sampidevkit/PIC32DevKit/Docs/PIC32DevKit Diagram-PartNumber.png

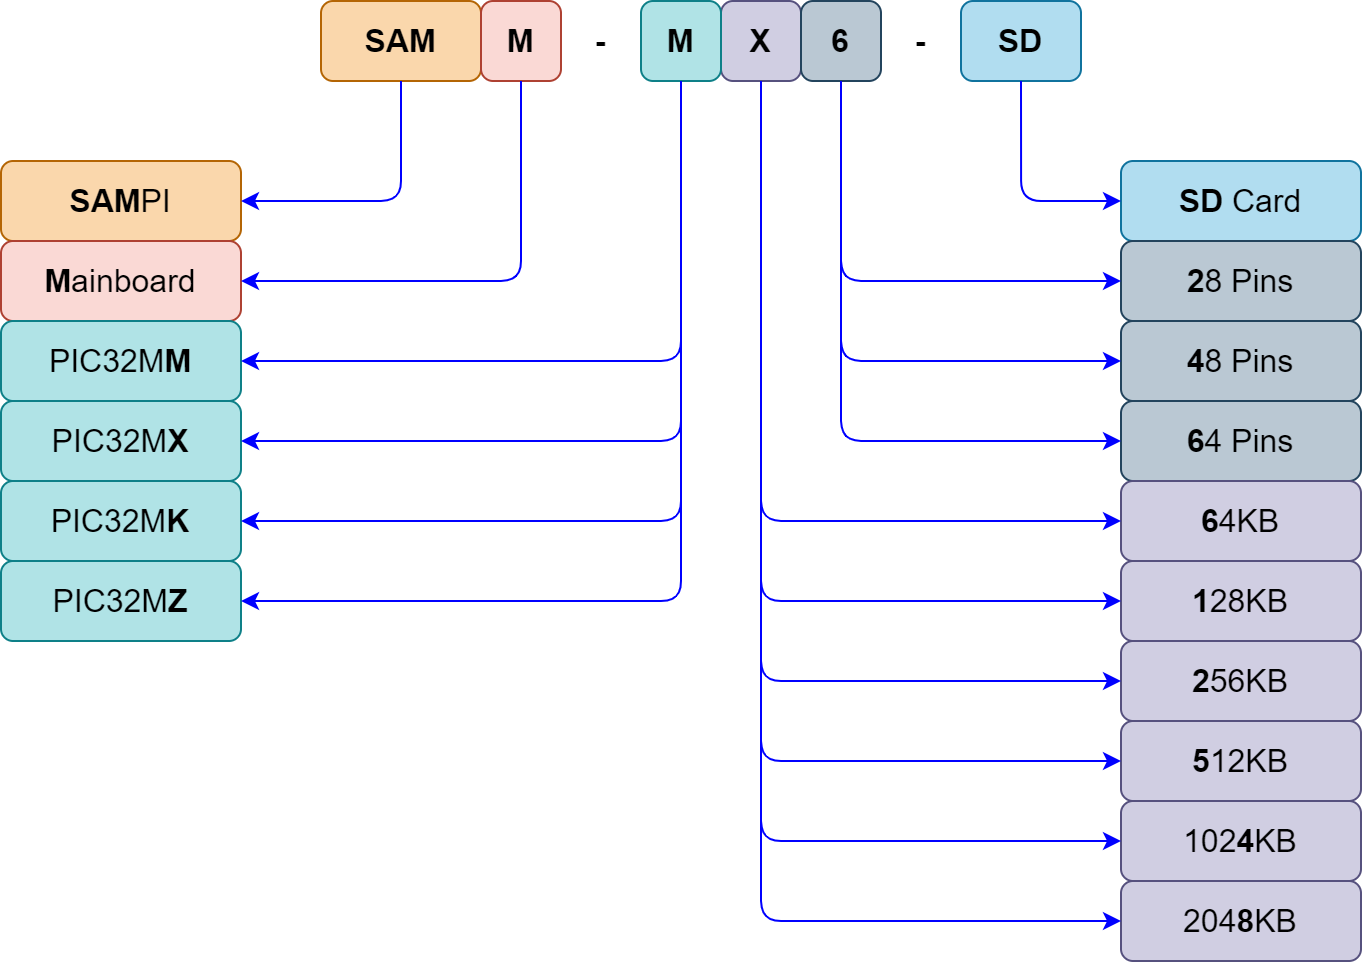
Docs/PIC32DevKit Diagram-PartNumber.png
