sampidevkit/PIC32DevKit/Docs/PIC32DevKit.png

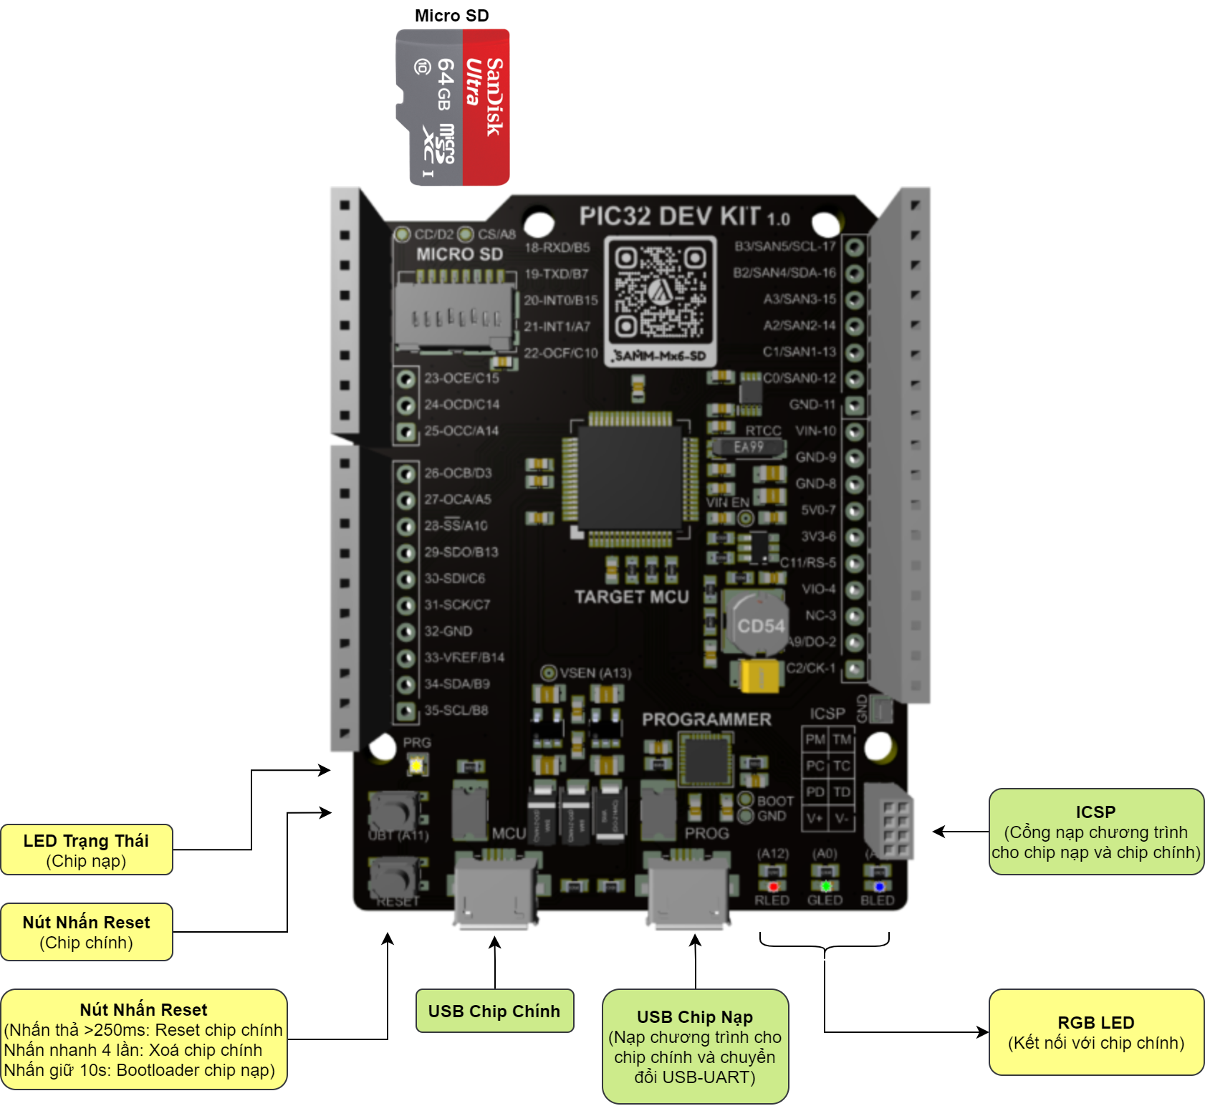
Docs/PIC32DevKit.png
