sampidevkit/PIC32DevKit/Docs/Ultra_microSDXC_UHS-I_Class10_64GB-retina.png

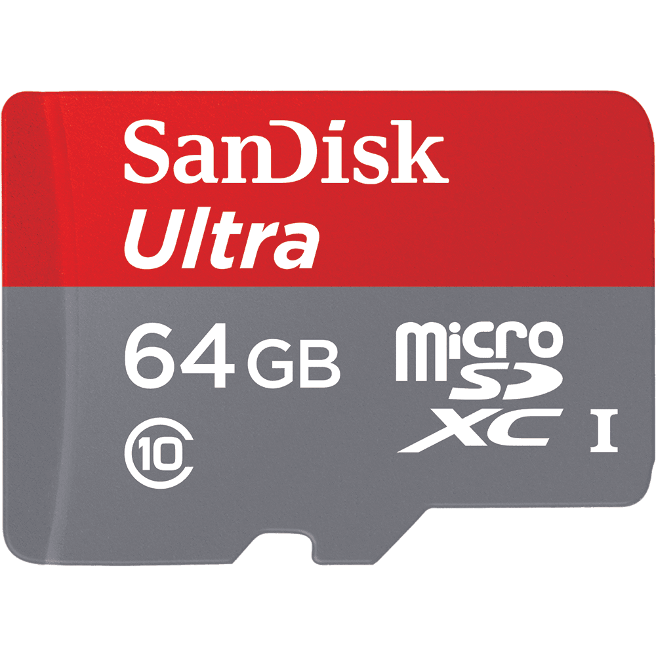
Docs/Ultra_microSDXC_UHS-I_Class10_64GB-retina.png
