sampidevkit/PIC32DevKit/HW/Product/V2.0/Picture/ScreenShot_20220208212343.png

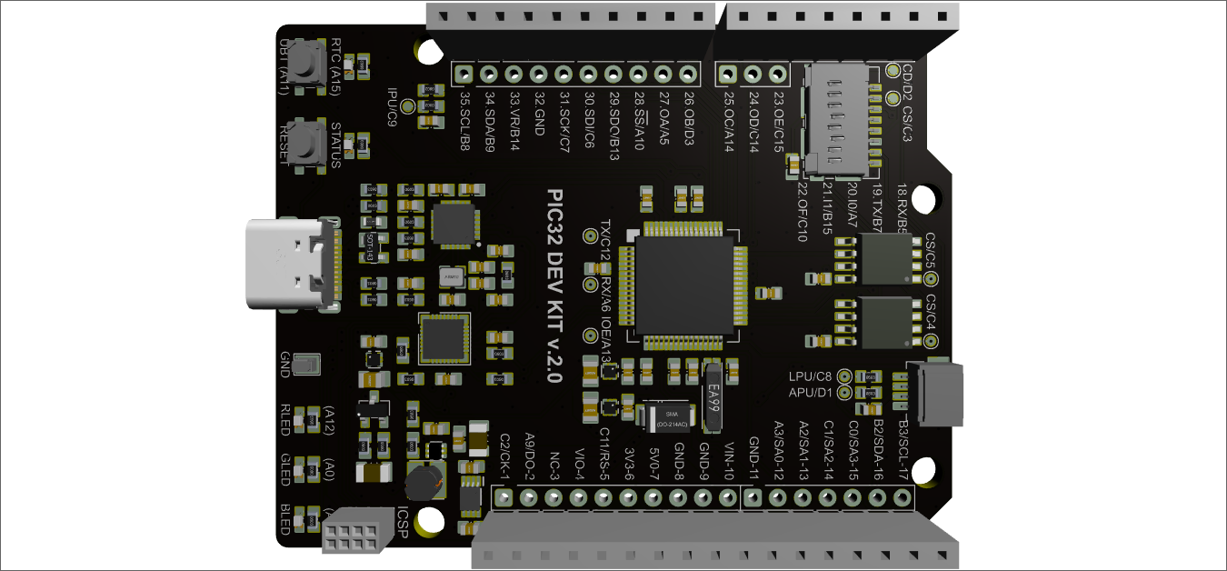
HW/Product/V2.0/Picture/ScreenShot_20220208212343.png
