sampidevkit/PIC32DevKit/FW/TG/Test.X/app/libcomp.h

#ifndef LIBCOMP_H
#define	LIBCOMP_H
/* *********************************************************** System Library */
#include <xc.h>
#include <time.h>
#include <stdint.h>
#include <stdbool.h>
/* ************************************************************** MCC Library */
#include "clc1.h"
#include "rtcc.h"
#include "clock.h"
#include "uart1.h"
#include "system.h"
#include "usb/usb.h"
#include "watchdog.h"
#include "coretimer.h"
#include "exceptions.h"
#include "pin_manager.h"
#include "spi1_driver.h"
#include "sd_spi/sd_spi.h"
#include "interrupt_manager.h"
#include "drivers/spi_master.h"
/* ************************************************************ SAMPI Library */
#include "Buttons/Buttons.h"
#include "Buttons/ButtonApi.h"
#include "Common/LibDef.h"
#include "Common/UserFunctions.h"
#include "Kit/kit.h"
#include "Kit/kit_usb_device.h"
#include "Kit/kit_usb_device_msd.h"
#include "System/TaskManager.h"
#include "System/TickTimer.h"
#include "System/Wdt.h"
#include "USB/usb_device_msd.h"

// Clock sources
#define SYS_CLK                         24000000UL
#define PB_CLK                          12000000UL
#define CORETIMER_CLK                   12000000UL
// Global interrupt
#define Disable_Global_Interrupt()      __builtin_disable_interrupts()
#define Enable_Global_Interrupt()       __builtin_enable_interrupts()
// Peripheral interrupt
#define Disable_Peripheral_Interrupt()  // Not implemented in PIC32
#define Enable_Peripheral_Interrupt()   // Not implemented in PIC32
// Core timer interrupt
#define Disable_Coretimer_Interrupt()   (IEC0CLR=_IEC0_CTIE_MASK)
#define Enable_Coretimer_Interrupt()    (IEC0SET=_IEC0_CTIE_MASK)
#define Clear_Coretimer_Interrupt()     (IFS0CLR=_IFS0_CTIF_MASK)

public void DummyInterruptHandler(void);
public void LibComp_Initialize(void);
public bool Button_GetState(void);
    
#endif
